MOSH-Insa-Toulouse/2021-2022_Ribette_Fees-/Draft2.asc

C1: cap; 100n
C2: cap; 100n
C3: cap; 100n
C4: cap; 1µ
R0: res; {Rsensor}
R1: res; 100k
R2: res; 33
R3: res; 270k
R5: res; 10k
R6: res; 1k
Rvar: res; {Rvar}
U1: LTC1050
Valim: voltage; 5
Named nets: Vout, 0, +5V, V-
.step param Rsensor 1000k 20000k 1000k
.op
.step param Rvar 1k 51k 10k
